rusefi/stim/boards/digital_inputs-a/board/misc/digital_inputs-a-outline.png

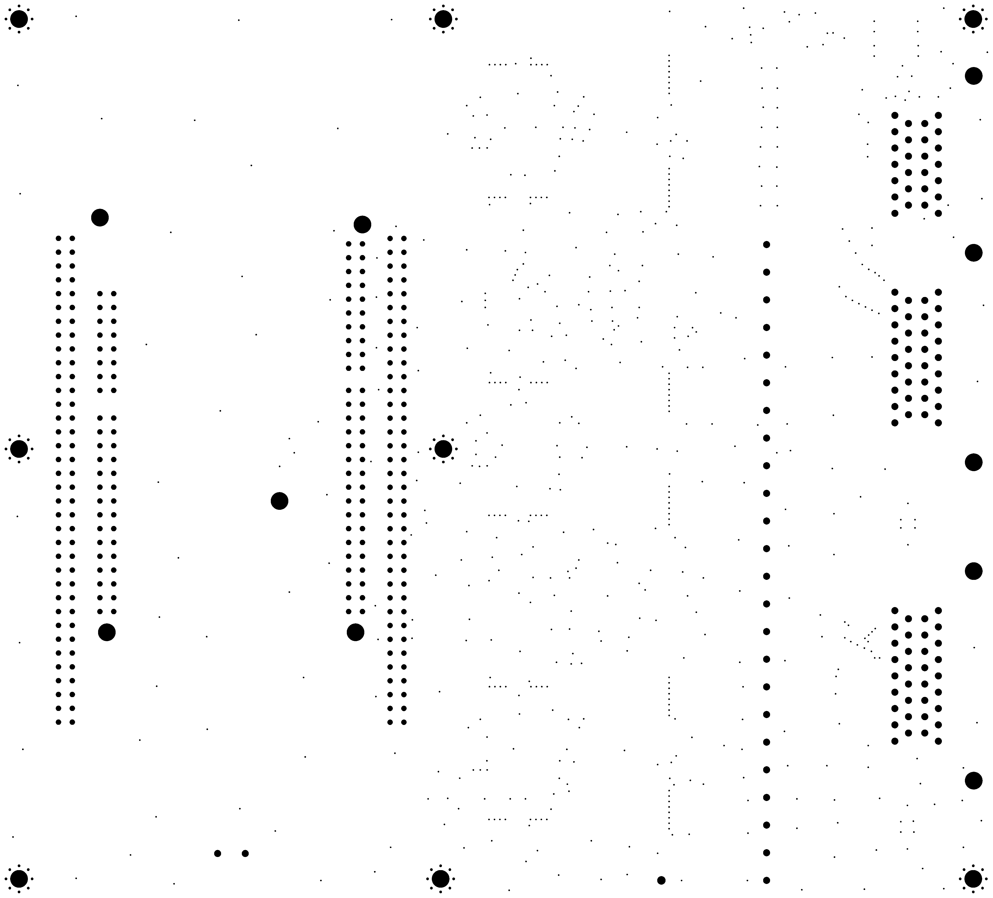
boards/digital_inputs-a/board/misc/digital_inputs-a-outline.png
