rusefi/stim/boards/digital_inputs-a/board/misc/digital_inputs-a-top.png

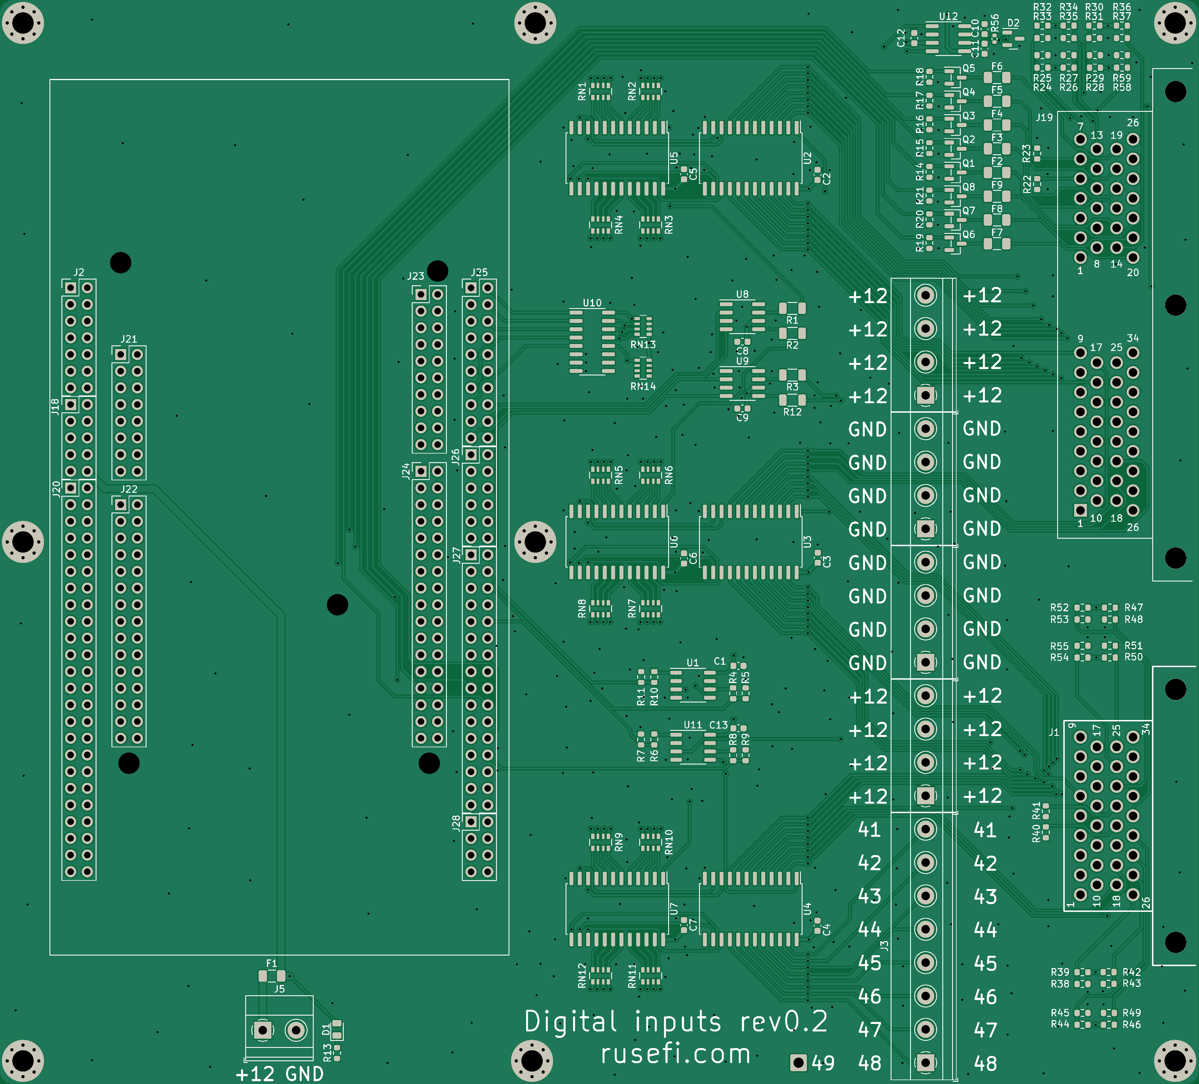
boards/digital_inputs-a/board/misc/digital_inputs-a-top.png
