rusefi/stim/boards/digital_inputs-c/board/digital_inputs-c.png

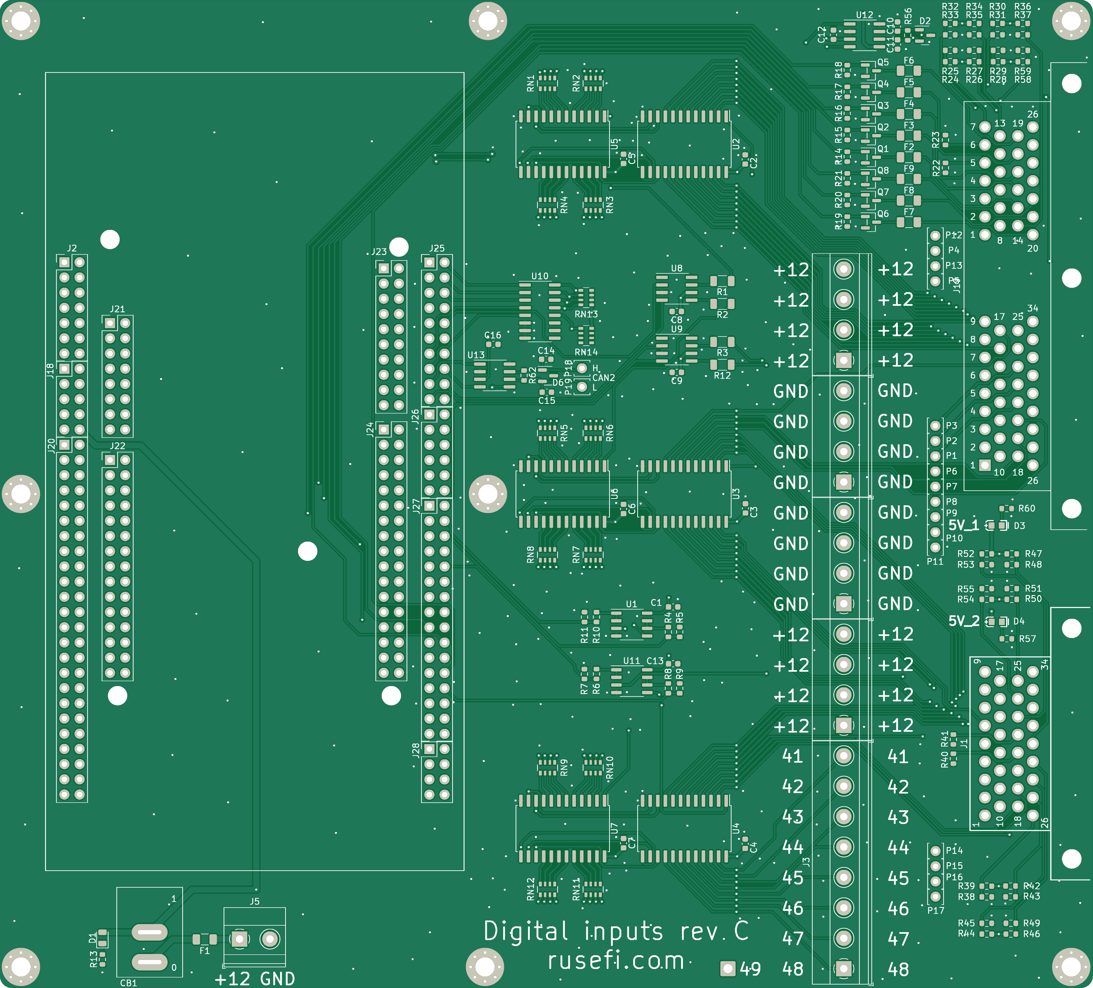
boards/digital_inputs-c/board/digital_inputs-c.png
