rusefi/stim/boards/digital_inputs-c/board/misc/digital_inputs-c-bottom.png

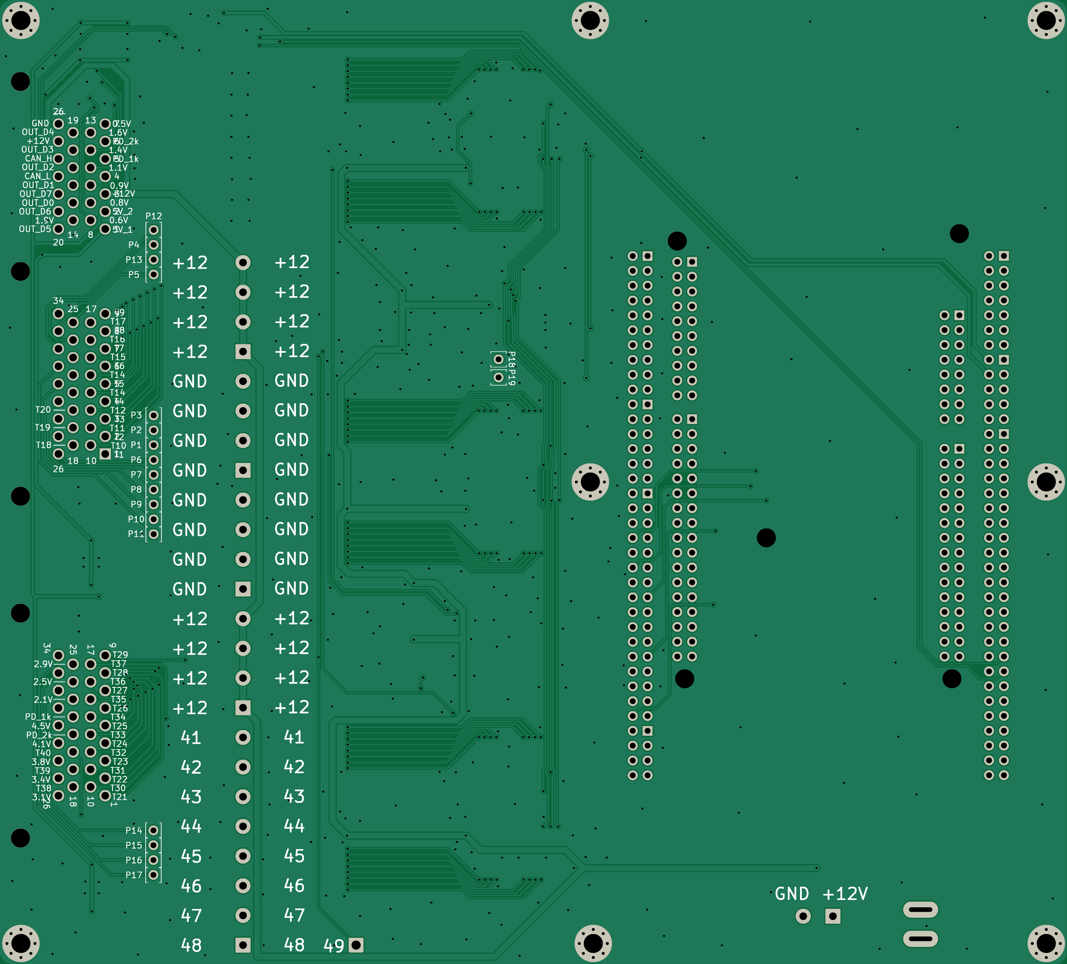
boards/digital_inputs-c/board/misc/digital_inputs-c-bottom.png
