rusefi/stim/boards/digital_inputs-c/board/misc/digital_inputs-c-top.png

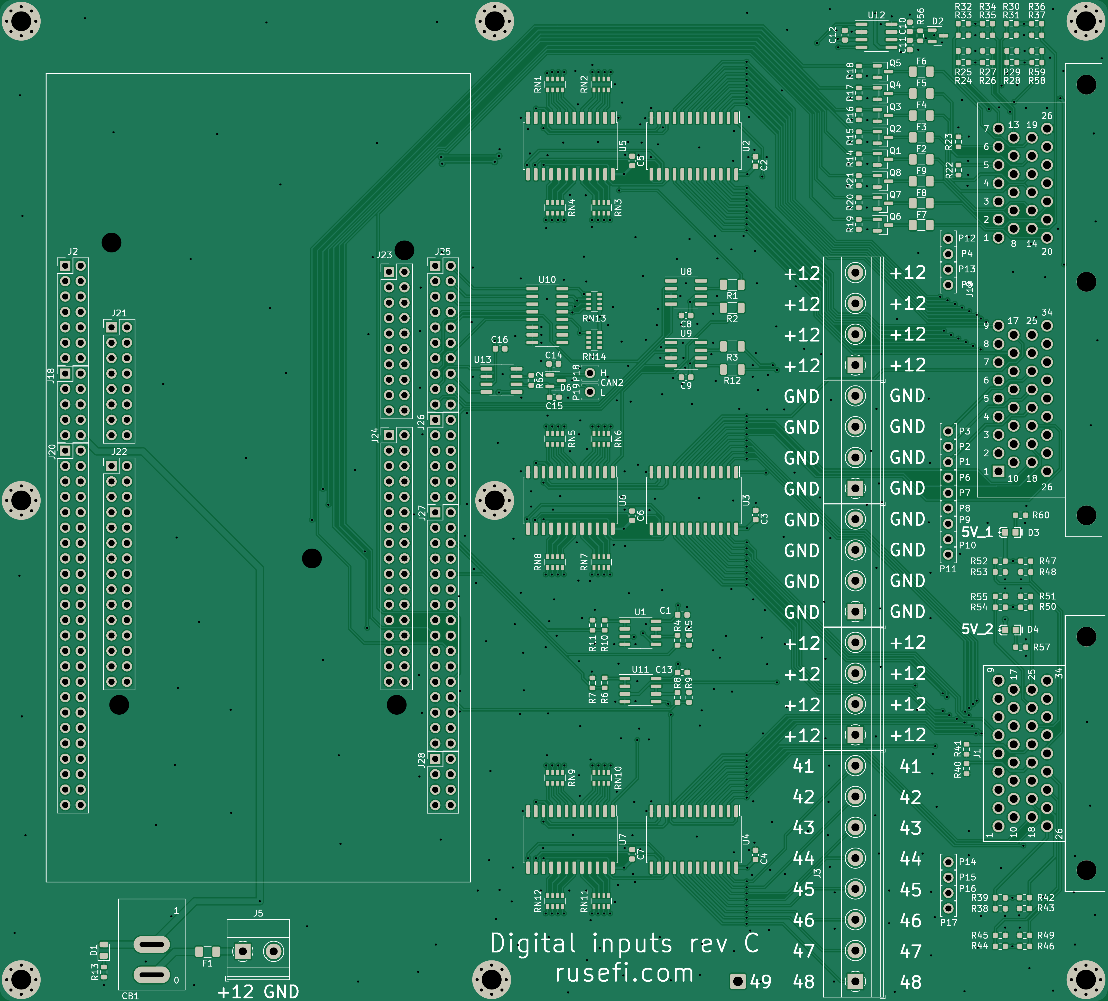
boards/digital_inputs-c/board/misc/digital_inputs-c-top.png
